omer-re/Sababox/Editor's choice of the day/mainpage_shot.jpg

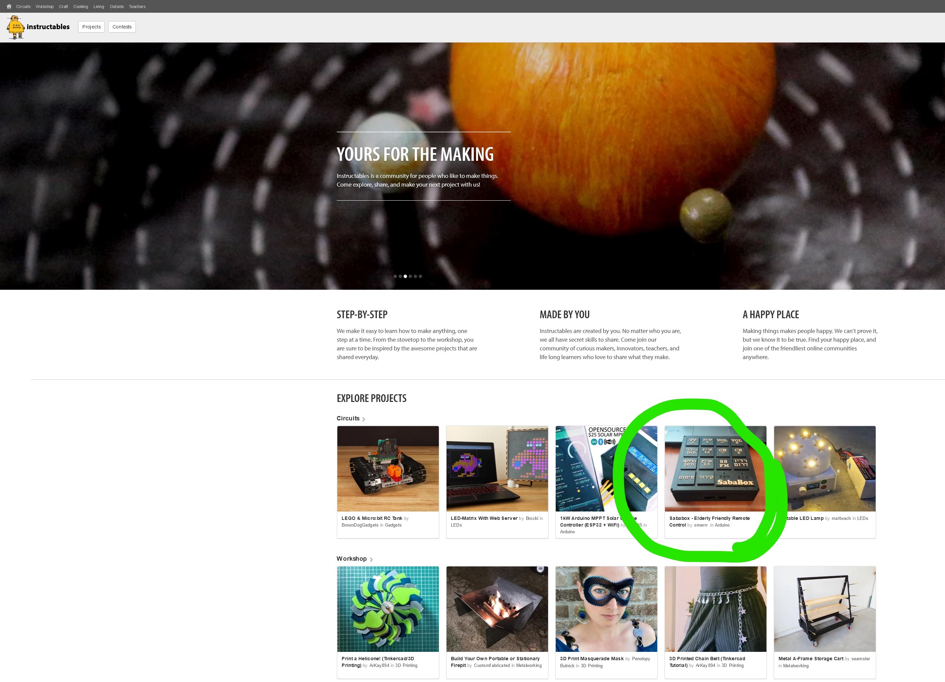
Editor's choice of the day/mainpage_shot.jpg
