omer-re/Sababox/Images/breadboard prototype.png

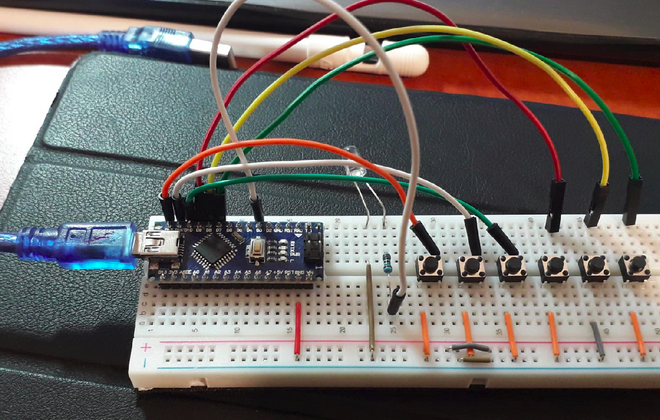
Images/breadboard prototype.png
