omer-re/Sababox/Images/Circuit sketch.jpeg

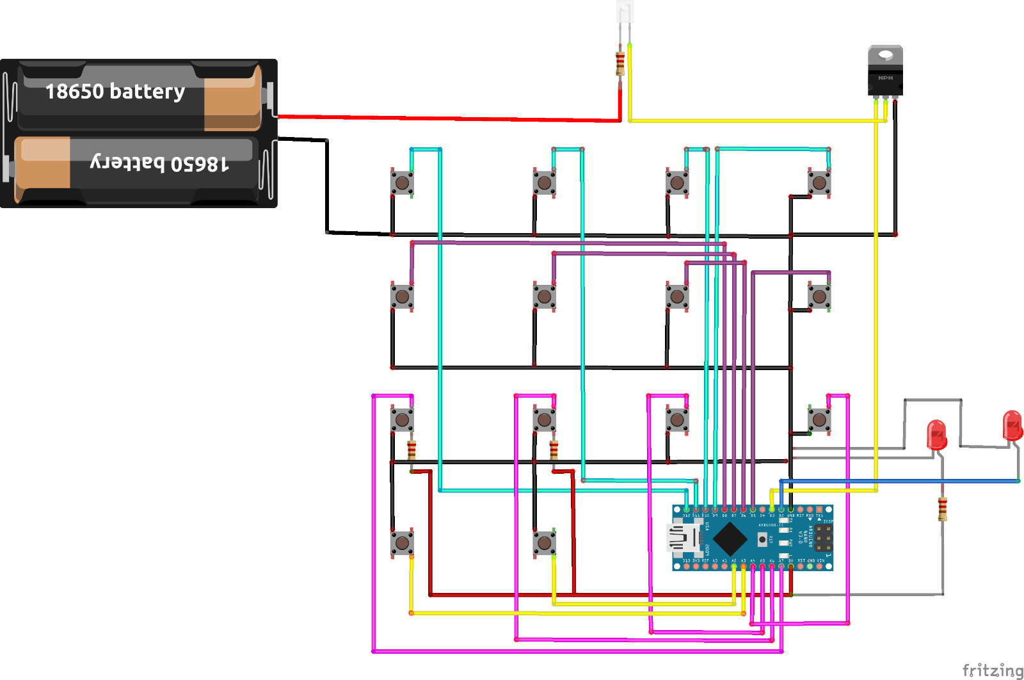
Images/Circuit sketch.jpeg
