omer-re/Sababox/Images/IDE settings.png

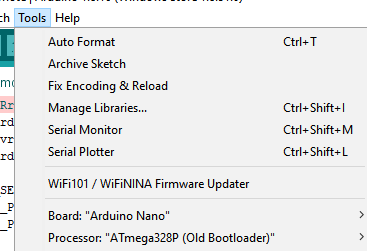
Images/IDE settings.png
