omer-re/Sababox/Images/screws zoom in.png

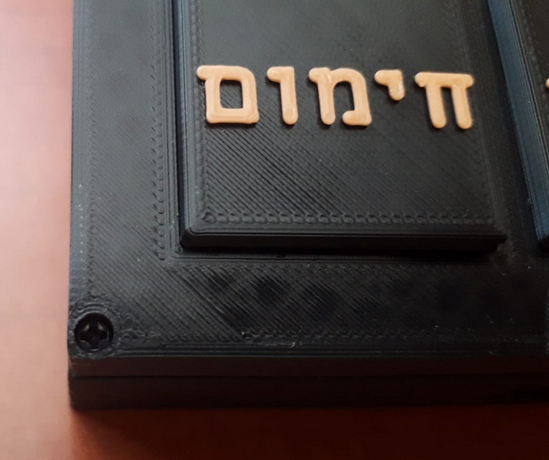
Images/screws zoom in.png
