omer-re/Sababox/Images/sketch on breadboard.png

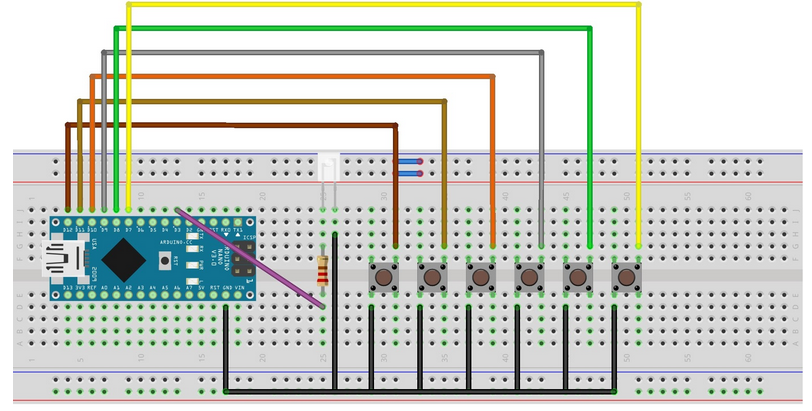
Images/sketch on breadboard.png
