omer-re/Sababox/Images/Tx led holes.png

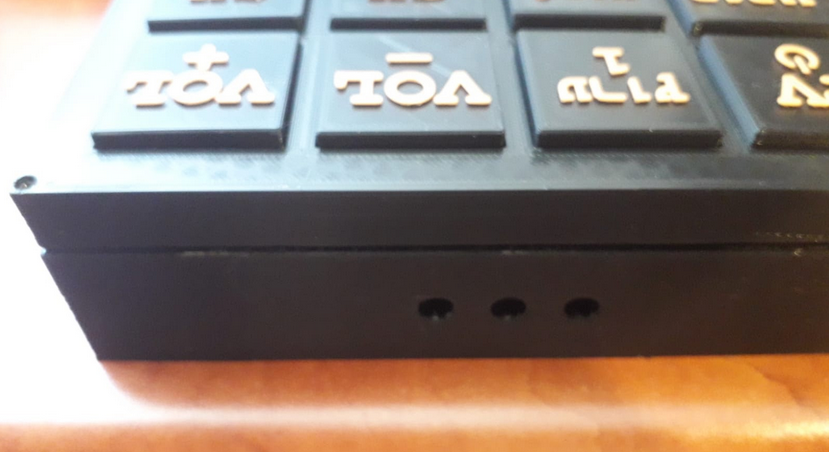
Images/Tx led holes.png
