omer-re/Sababox/IRremote/src/IRremoteInt.h

/**
 * @file IRremoteInt.h
 * @brief Contains all declarations required for the internal functions.
 *
 * This file is part of Arduino-IRremote https://github.com/Arduino-IRremote/Arduino-IRremote.
 *
 *
 ************************************************************************************
 * MIT License
 *
 * Copyright (c) 2015-2021 Ken Shirriff http://www.righto.com, Rafi Khan, Armin Joachimsmeyer
 *
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
 ************************************************************************************
 */
#ifndef IRremoteInt_h
#define IRremoteInt_h

#include <Arduino.h>

#if ! defined(RAW_BUFFER_LENGTH)
//#define RAW_BUFFER_LENGTH  100  ///< Maximum length of raw duration buffer. Must be even. 100 supports up to 48 bit codings inclusive 1 start and 1 stop bit.
#define RAW_BUFFER_LENGTH  220  ///< Maximum length of raw duration buffer. Must be even. 100 supports up to 48 bit codings inclusive 1 start and 1 stop bit.
#endif
#if RAW_BUFFER_LENGTH % 2 == 1
#error RAW_BUFFER_LENGTH must be even, since the array consists of space / mark pairs.
#endif

#define MARK   1
#define SPACE  0

/**
 * For better readability of code
 */
#define DISABLE_LED_FEEDBACK false
#define ENABLE_LED_FEEDBACK true
#define USE_DEFAULT_FEEDBACK_LED_PIN 0

#include "IRProtocol.h"

/****************************************************
 * Declarations for the receiver Interrupt Service Routine
 ****************************************************/
// ISR State-Machine : Receiver States
#define IR_REC_STATE_IDLE      0
#define IR_REC_STATE_MARK      1
#define IR_REC_STATE_SPACE     2
#define IR_REC_STATE_STOP      3

/**
 * This struct contains the data and control used for receiver static functions and the ISR (interrupt service routine)
 * Only StateForISR needs to be volatile. All the other fields are not written by ISR after data available and before start/resume.
 */
struct irparams_struct {
    // The fields are ordered to reduce memory over caused by struct-padding
    volatile uint8_t StateForISR;   ///< State Machine state
    uint8_t IRReceivePin;           ///< Pin connected to IR data from detector
#if defined(__AVR__)
    volatile uint8_t *IRReceivePinPortInputRegister;
    uint8_t IRReceivePinMask;
#endif
    uint16_t TickCounterForISR;     ///< Counts 50uS ticks. The value is copied into the rawbuf array on every transition.

    bool OverflowFlag;              ///< Raw buffer OverflowFlag occurred
#if RAW_BUFFER_LENGTH <= 255        // saves around 75 bytes program space and speeds up ISR
    uint8_t rawlen;                 ///< counter of entries in rawbuf
#else
    unsigned int rawlen;            ///< counter of entries in rawbuf
#endif
    uint16_t rawbuf[RAW_BUFFER_LENGTH]; ///< raw data / tick counts per mark/space, first entry is the length of the gap between previous and current command
};

//#define DEBUG // Activate this for lots of lovely debug output from the IRremote core and all protocol decoders.
//#define TRACE // Activate this for more debug output.
/*
 * Debug directives
 */
#ifdef DEBUG
#  define DEBUG_PRINT(...)    Serial.print(__VA_ARGS__)
#  define DEBUG_PRINTLN(...)  Serial.println(__VA_ARGS__)
#else
/**
 * If DEBUG, print the arguments, otherwise do nothing.
 */
#  define DEBUG_PRINT(...) void()
/**
 * If DEBUG, print the arguments as a line, otherwise do nothing.
 */
#  define DEBUG_PRINTLN(...) void()
#endif

#ifdef TRACE
#  define TRACE_PRINT(...)    Serial.print(__VA_ARGS__)
#  define TRACE_PRINTLN(...)  Serial.println(__VA_ARGS__)
#else
#  define TRACE_PRINT(...) void()
#  define TRACE_PRINTLN(...) void()
#endif

#if (__GNUC__ > 4) || (__GNUC__ == 4 && __GNUC_MINOR__ >= 4)
#define COMPILER_HAS_PRAGMA_MESSAGE
#endif

/****************************************************
 *                     RECEIVING
 ****************************************************/
/*
 * Activating this saves 60 bytes program space and 14 bytes RAM
 */
//#define NO_LEGACY_COMPATIBILITY
#if !defined(NO_LEGACY_COMPATIBILITY)
/**
 * Results returned from old decoders !!!deprecated!!!
 */
struct decode_results {
    decode_type_t decode_type;  // deprecated, moved to decodedIRData.protocol ///< UNKNOWN, NEC, SONY, RC5, ...
    uint16_t address;           ///< Used by Panasonic & Sharp [16-bits]
    uint32_t value;             // deprecated, moved to decodedIRData.decodedRawData ///< Decoded value / command [max 32-bits]
    uint8_t bits;               // deprecated, moved to decodedIRData.numberOfBits ///< Number of bits in decoded value
    uint16_t magnitude;         // deprecated, moved to decodedIRData.extra ///< Used by MagiQuest [16-bits]
    bool isRepeat;              // deprecated, moved to decodedIRData.flags ///< True if repeat of value is detected

// next 3 values are copies of irparams values - see IRremoteint.h
    uint16_t *rawbuf;           // deprecated, moved to decodedIRData.rawDataPtr->rawbuf ///< Raw intervals in 50uS ticks
    uint16_t rawlen;            // deprecated, moved to decodedIRData.rawDataPtr->rawlen ///< Number of records in rawbuf
    bool overflow;              // deprecated, moved to decodedIRData.flags ///< true if IR raw code too long
};
#endif

/*
 * Definitions for member IRData.flags
 */
#define IRDATA_FLAGS_EMPTY              0x00
#define IRDATA_FLAGS_IS_REPEAT          0x01
#define IRDATA_FLAGS_IS_AUTO_REPEAT     0x02
#define IRDATA_FLAGS_PARITY_FAILED      0x04 ///< the current (autorepeat) frame violated parity check
#define IRDATA_TOGGLE_BIT_MASK          0x08
#define IRDATA_FLAGS_EXTRA_INFO         0x10 ///< there is unexpected extra info not contained in address and data (e.g. Kaseikyo unknown vendor ID)
#define IRDATA_FLAGS_WAS_OVERFLOW       0x40 ///< irparams.rawlen is 0 in this case to avoid endless OverflowFlag
#define IRDATA_FLAGS_IS_LSB_FIRST       0x00
#define IRDATA_FLAGS_IS_MSB_FIRST       0x80 ///< Just for info. Value is simply determined by the protocol

/**
 * Data structure for the user application, available as decodedIRData.
 * Filled by decoders and read by print functions or user application.
 */
struct IRData {
    decode_type_t protocol;     ///< UNKNOWN, NEC, SONY, RC5, ...
    uint16_t address;           ///< Decoded address
    uint16_t command;           ///< Decoded command
    uint16_t extra;             ///< Used by MagiQuest and for Kaseikyo unknown vendor ID.  Ticks used for decoding Distance protocol.
    uint8_t numberOfBits; ///< Number of bits received for data (address + command + parity) - to determine protocol length if different length are possible.
    uint8_t flags;              ///< See IRDATA_FLAGS_* definitions above
    uint32_t decodedRawData;    ///< Up to 32 bit decoded raw data, used for sendRaw functions.
    irparams_struct *rawDataPtr; ///< Pointer of the raw timing data to be decoded. Mainly the data buffer filled by receiving ISR.
};

/**
 * Just for better readability of code
 */
#define USE_DEFAULT_FEEDBACK_LED_PIN 0

/**
 * Main class for receiving IR signals
 */
class IRrecv {
public:

    IRrecv();
    IRrecv(uint8_t aReceivePin);
    IRrecv(uint8_t aReceivePin, uint8_t aFeedbackLEDPin);
    void setReceivePin(uint8_t aReceivePinNumber);

    void enableIRIn();
    void disableIRIn();

    /*
     * Stream like API
     */
    void begin(uint8_t aReceivePin, bool aEnableLEDFeedback = false, uint8_t aFeedbackLEDPin = USE_DEFAULT_FEEDBACK_LED_PIN);
    void start(); // alias for enableIRIn
    void start(uint16_t aMicrosecondsToAddToGapCounter);
    bool available();
    IRData* read(); // returns decoded data
    // write is a method of class IRsend below
    // size_t write(IRData *aIRSendData, uint_fast8_t aNumberOfRepeats = NO_REPEATS);
    void stop(); // alias for disableIRIn
    void end();

    bool isIdle();

    /*
     * The main functions
     */
    bool decode();  // Check if available and try to decode
    void resume();  // Enable receiving of the next value

    /*
     * Useful info and print functions
     */
    void printIRResultShort(Print *aSerial);
    void printIRResultMinimal(Print *aSerial);
    void printIRResultRawFormatted(Print *aSerial, bool aOutputMicrosecondsInsteadOfTicks = true);
    void printIRResultAsCVariables(Print *aSerial);

    void compensateAndPrintIRResultAsCArray(Print *aSerial, String sig_name, bool aOutputMicrosecondsInsteadOfTicks = true);
    void compensateAndPrintIRResultAsPronto(Print *aSerial, unsigned int frequency = 38000U);

    /*
     * Store the data for further processing
     */
    void compensateAndStoreIRResultInArray(uint8_t *aArrayPtr);
    size_t compensateAndStorePronto(String *aString, unsigned int frequency = 38000U);

    /*
     * The main decoding functions used by the individual decoders
     */
    bool decodePulseDistanceData(uint8_t aNumberOfBits, uint8_t aStartOffset, uint16_t aBitMarkMicros, uint16_t aOneSpaceMicros,
            uint16_t aZeroSpaceMicros, bool aMSBfirst);

    bool decodePulseWidthData(uint8_t aNumberOfBits, uint8_t aStartOffset, uint16_t aOneMarkMicros, uint16_t aZeroMarkMicros,
            uint16_t aBitSpaceMicros, bool aMSBfirst);

    bool decodeBiPhaseData(uint_fast8_t aNumberOfBits, uint_fast8_t aStartOffset, uint_fast8_t aStartClockCount,
            uint_fast8_t aValueOfSpaceToMarkTransition, uint16_t aBiphaseTimeUnit);

    void initBiphaselevel(uint8_t aRCDecodeRawbuffOffset, uint16_t aBiphaseTimeUnit);
    uint8_t getBiphaselevel();

    /*
     * All standard (decode address + command) protocol decoders
     */
    bool decodeBoseWave();
    bool decodeDenon();
    bool decodeJVC();
    bool decodeKaseikyo();
    bool decodeLegoPowerFunctions();
    bool decodeLG();
    bool decodeMagiQuest(); // not completely standard
    bool decodeNEC();
    bool decodeRC5();
    bool decodeRC6();
    bool decodeSamsung();
    bool decodeSharp(); // redirected to decodeDenon()
    bool decodeSony();

    bool decodeDistance();

    bool decodeHash();

    // Template function :-)
    bool decodeShuzu();

    /*
     * Old functions
     */
#if !defined(NO_LEGACY_COMPATIBILITY)
    bool decodeDenonOld(decode_results *aResults);
    bool decodeJVCMSB(decode_results *aResults);
    bool decodeLGMSB(decode_results *aResults);
    bool decodeNECMSB(decode_results *aResults);
    bool decodePanasonicMSB(decode_results *aResults);
    bool decodeSonyMSB(decode_results *aResults);
    bool decodeSAMSUNG(decode_results *aResults);
    bool decodeHashOld(decode_results *aResults);

    bool decode(
            decode_results *aResults)
                    __attribute__ ((deprecated ("Please use IrReceiver.decode() without a parameter and IrReceiver.decodedIRData.<fieldname> ."))); // deprecated
#endif
    bool decodeWhynter();

    /*
     * Internal functions
     */
    void initDecodedIRData();
    uint8_t compare(unsigned int oldval, unsigned int newval);

    IRData decodedIRData;       // New: decoded IR data for the application

    // Last decoded IR data for repeat detection
    decode_type_t lastDecodedProtocol;
    uint32_t lastDecodedAddress;
    uint32_t lastDecodedCommand;

    uint8_t repeatCount;        // Used e.g. for Denon decode for autorepeat decoding.
};

extern uint8_t sBiphaseDecodeRawbuffOffset; //

/*
 * Mark & Space matching functions
 */
bool matchTicks(uint16_t aMeasuredTicks, uint16_t aMatchValueMicros);
bool matchMark(uint16_t aMeasuredTicks, uint16_t aMatchValueMicros);
bool matchSpace(uint16_t aMeasuredTicks, uint16_t aMatchValueMicros);

/*
 * Old function names
 */
bool MATCH(uint16_t measured, uint16_t desired);
bool MATCH_MARK(uint16_t measured_ticks, uint16_t desired_us);
bool MATCH_SPACE(uint16_t measured_ticks, uint16_t desired_us);

int getMarkExcessMicros();

void printIRResultShort(Print *aSerial, IRData *aIRDataPtr, uint16_t aLeadingSpaceDuration = 0);

/****************************************************
 * Feedback LED related functions
 ****************************************************/
void setFeedbackLED(bool aSwitchLedOn);
void setLEDFeedback(uint8_t aFeedbackLEDPin, bool aEnableLEDFeedback); // if aFeedbackLEDPin == 0, then take board BLINKLED_ON() and BLINKLED_OFF() functions
void enableLEDFeedback();
void disableLEDFeedback();

void blink13(bool aEnableLEDFeedback)
        __attribute__ ((deprecated ("Please use setLEDFeedback() or enableLEDFeedback() / disableLEDFeedback."))); // deprecated
void setBlinkPin(uint8_t aFeedbackLEDPin) __attribute__ ((deprecated ("Please use setLEDFeedback()."))); // deprecated

/**
 * microseconds per clock interrupt tick
 */
#if ! defined(MICROS_PER_TICK)
#define MICROS_PER_TICK    50
#endif

/*
 * Pulse parms are ((X*50)-100) for the Mark and ((X*50)+100) for the Space.
 * First MARK is the one after the long gap
 * Pulse parameters in uSec
 */
/** Relative tolerance (in percent) for some comparisons on measured data. */
#define TOLERANCE       25

/** Lower tolerance for comparison of measured data */
//#define LTOL            (1.0 - (TOLERANCE/100.))
#define LTOL            (100 - TOLERANCE)
/** Upper tolerance for comparison of measured data */
//#define UTOL            (1.0 + (TOLERANCE/100.))
#define UTOL            (100 + TOLERANCE)

//#define TICKS_LOW(us)   ((int)(((us)*LTOL/MICROS_PER_TICK)))
//#define TICKS_HIGH(us)  ((int)(((us)*UTOL/MICROS_PER_TICK + 1)))
#if MICROS_PER_TICK == 50 && TOLERANCE == 25           // Defaults
#define TICKS_LOW(us)   ((us)/67 )     // (us) / ((MICROS_PER_TICK:50 / LTOL:75 ) * 100)
#define TICKS_HIGH(us)  ((us)/40 + 1)  // (us) / ((MICROS_PER_TICK:50 / UTOL:125) * 100) + 1
#else
    #define TICKS_LOW(us)   ((uint16_t) ((long) (us) * LTOL / (MICROS_PER_TICK * 100) ))
    #define TICKS_HIGH(us)  ((uint16_t) ((long) (us) * UTOL / (MICROS_PER_TICK * 100) + 1))
#endif

/*
 * The receiver instance
 */
extern IRrecv IrReceiver;

/****************************************************
 *                     SENDING
 ****************************************************/

/**
 * Just for better readability of code
 */
#define NO_REPEATS  0
#define SEND_STOP_BIT true
#define SEND_REPEAT_COMMAND true ///< used for e.g. NEC, where a repeat is different from just repeating the data.

/**
 * Duty cycle in percent for sent signals.
 */
#if ! defined(IR_SEND_DUTY_CYCLE)
#define IR_SEND_DUTY_CYCLE 30 // 30 saves power and is compatible to the old existing code
#endif

/**
 * Main class for sending IR signals
 */
class IRsend {
public:
    IRsend(uint8_t aSendPin);
    void setSendPin(uint8_t aSendPinNumber);
    void begin(uint8_t aSendPin, bool aEnableLEDFeedback = true, uint8_t aFeedbackLEDPin = USE_DEFAULT_FEEDBACK_LED_PIN);

    IRsend();
    void begin(bool aEnableLEDFeedback, uint8_t aFeedbackLEDPin = USE_DEFAULT_FEEDBACK_LED_PIN)
            __attribute__ ((deprecated ("Please use begin(<sendPin>, <EnableLEDFeedback>, <LEDFeedbackPin>)")));

    size_t write(IRData *aIRSendData, uint_fast8_t aNumberOfRepeats = NO_REPEATS);

    void enableIROut(uint8_t aFrequencyKHz);

    void sendPulseDistanceWidthData(unsigned int aOneMarkMicros, unsigned int aOneSpaceMicros, unsigned int aZeroMarkMicros,
            unsigned int aZeroSpaceMicros, uint32_t aData, uint8_t aNumberOfBits, bool aMSBfirst, bool aSendStopBit = false);
    void sendBiphaseData(unsigned int aBiphaseTimeUnit, uint32_t aData, uint_fast8_t aNumberOfBits);

    void mark(unsigned int aMarkMicros);
    void space(unsigned int aSpaceMicros);
    void IRLedOff();

// 8 Bit array
    void sendRaw(const uint8_t aBufferWithTicks[], uint_fast8_t aLengthOfBuffer, uint_fast8_t aIRFrequencyKilohertz);
    void sendRaw_P(const uint8_t aBufferWithTicks[], uint_fast8_t aLengthOfBuffer, uint_fast8_t aIRFrequencyKilohertz);

// 16 Bit array
    void sendRaw(const uint16_t aBufferWithMicroseconds[], uint_fast8_t aLengthOfBuffer, uint_fast8_t aIRFrequencyKilohertz);
    void sendRaw_P(const uint16_t aBufferWithMicroseconds[], uint_fast8_t aLengthOfBuffer, uint_fast8_t aIRFrequencyKilohertz);

    /*
     * New send functions
     */
    void sendBoseWave(uint8_t aCommand, uint_fast8_t aNumberOfRepeats = NO_REPEATS);
    void sendDenon(uint8_t aAddress, uint8_t aCommand, uint_fast8_t aNumberOfRepeats, bool aSendSharp = false);
    void sendDenonRaw(uint16_t aRawData, uint_fast8_t aNumberOfRepeats = 0)
            __attribute__ ((deprecated ("Please use sendDenon(aAddress, aCommand, aNumberOfRepeats).")));
    void sendJVC(uint8_t aAddress, uint8_t aCommand, uint_fast8_t aNumberOfRepeats);

    void sendLGRepeat();
    void sendLG(uint8_t aAddress, uint16_t aCommand, uint_fast8_t aNumberOfRepeats, bool aIsRepeat = false);
    void sendLGRaw(uint32_t aRawData, uint_fast8_t aNumberOfRepeats = 0, bool aIsRepeat = false);

    void sendNECRepeat();
    void sendNEC(uint16_t aAddress, uint8_t aCommand, uint_fast8_t aNumberOfRepeats, bool aIsRepeat = false);
    void sendNECRaw(uint32_t aRawData, uint_fast8_t aNumberOfRepeats = 0, bool aIsRepeat = false);
    // NEC variants
    void sendOnkyo(uint16_t aAddress, uint16_t aCommand, uint_fast8_t aNumberOfRepeats, bool aIsRepeat = false);
    void sendApple(uint8_t aAddress, uint8_t aCommand, uint_fast8_t aNumberOfRepeats, bool aIsRepeat = false);

    void sendPanasonic(uint16_t aAddress, uint8_t aData, uint_fast8_t aNumberOfRepeats); // LSB first
    void sendKaseikyo(uint16_t aAddress, uint8_t aData, uint_fast8_t aNumberOfRepeats, uint16_t aVendorCode); // LSB first

    void sendRC5(uint8_t aAddress, uint8_t aCommand, uint_fast8_t aNumberOfRepeats, bool aEnableAutomaticToggle = true);
    void sendRC6(uint8_t aAddress, uint8_t aCommand, uint_fast8_t aNumberOfRepeats, bool aEnableAutomaticToggle = true);
    void sendSamsungRepeat();
    void sendSamsung(uint16_t aAddress, uint16_t aCommand, uint_fast8_t aNumberOfRepeats, bool aIsRepeat = false);
    void sendSharp(uint8_t aAddress, uint8_t aCommand, uint_fast8_t aNumberOfRepeats); // redirected to sendDenon
    void sendSony(uint16_t aAddress, uint8_t aCommand, uint_fast8_t aNumberOfRepeats, uint8_t numberOfBits = SIRCS_12_PROTOCOL);

    void sendLegoPowerFunctions(uint8_t aChannel, uint8_t tCommand, uint8_t aMode, bool aDoSend5Times = true);
    void sendLegoPowerFunctions(uint16_t aRawData, bool aDoSend5Times = true);
    void sendLegoPowerFunctions(uint16_t aRawData, uint8_t aChannel, bool aDoSend5Times = true);

    void sendMagiQuest(uint32_t wand_id, uint16_t magnitude);

    void sendPronto(const __FlashStringHelper *str, uint_fast8_t aNumberOfRepeats = NO_REPEATS);
    void sendPronto(const char *prontoHexString, uint_fast8_t aNumberOfRepeats = NO_REPEATS);
    void sendPronto(const uint16_t *data, unsigned int length, uint_fast8_t aNumberOfRepeats = NO_REPEATS);
#if defined(__AVR__)
    void sendPronto_PF(uint_farptr_t str, uint_fast8_t aNumberOfRepeats = NO_REPEATS);
    void sendPronto_P(const char *str, uint_fast8_t aNumberOfRepeats);
#endif

// Template protocol :-)
    void sendShuzu(uint16_t aAddress, uint8_t aCommand, uint_fast8_t aNumberOfRepeats);

    /*
     * OLD send functions
     */
    void sendDenon(unsigned long data, int nbits);
    void sendDISH(unsigned long data, int nbits);
    void sendJVC(unsigned long data, int nbits,
            bool repeat)
                    __attribute__ ((deprecated ("This old function sends MSB first! Please use sendJVC(aAddress, aCommand, aNumberOfRepeats)."))) {
        sendJVCMSB(data, nbits, repeat);
    }
    void sendJVCMSB(unsigned long data, int nbits, bool repeat = false);

    void sendLG(unsigned long data, int nbits);

    void sendNEC(uint32_t aRawData,
            uint8_t nbits)
                    __attribute__ ((deprecated ("This old function sends MSB first! Please use sendNEC(aAddress, aCommand, aNumberOfRepeats)."))) {
        sendNECMSB(aRawData, nbits);
    }
    void sendNECMSB(uint32_t data, uint8_t nbits, bool repeat = false);
    void sendPanasonic(uint16_t aAddress,
            uint32_t aData)
                    __attribute__ ((deprecated ("This old function sends MSB first! Please use sendPanasonic(aAddress, aCommand, aNumberOfRepeats).")));
    void sendRC5(uint32_t data, uint8_t nbits);
    void sendRC5ext(uint8_t addr, uint8_t cmd, bool toggle);
    void sendRC6(uint32_t data, uint8_t nbits);
    void sendRC6(uint64_t data, uint8_t nbits);
    void sendSharpRaw(unsigned long data, int nbits);
    void sendSharp(unsigned int address, unsigned int command);
    void sendSAMSUNG(unsigned long data, int nbits);
    __attribute__ ((deprecated ("This old function sends MSB first! Please use sendSamsung().")));
    void sendSony(unsigned long data,
            int nbits)
                    __attribute__ ((deprecated ("This old function sends MSB first! Please use sendSony(aAddress, aCommand, aNumberOfRepeats).")));
    ;
    void sendWhynter(unsigned long data, int nbits);

    uint8_t sendPin;

    unsigned int periodTimeMicros;
    unsigned int periodOnTimeMicros; // compensated with PULSE_CORRECTION_NANOS for duration of digitalWrite.
    unsigned int getPulseCorrectionNanos();

    void customDelayMicroseconds(unsigned long aMicroseconds);
};

/*
 * The sender instance
 */
extern IRsend IrSender;

#endif // IRremoteInt_h

#pragma once
